open3dengineering/Prusa-i3/Manual/media/assembed_parts/x3.png

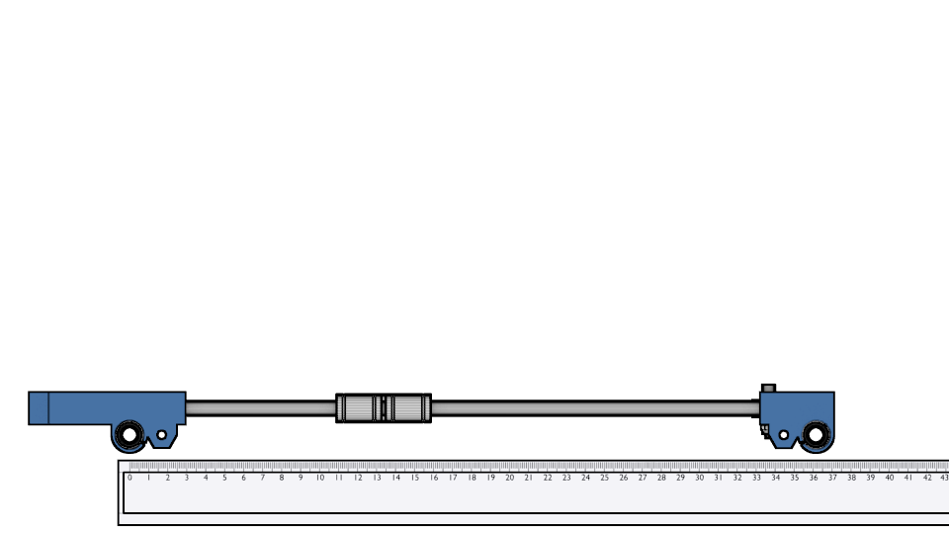
Manual/media/assembed_parts/x3.png
