open3dengineering/Prusa-i3/Manual/media/assembed_parts/x6.png

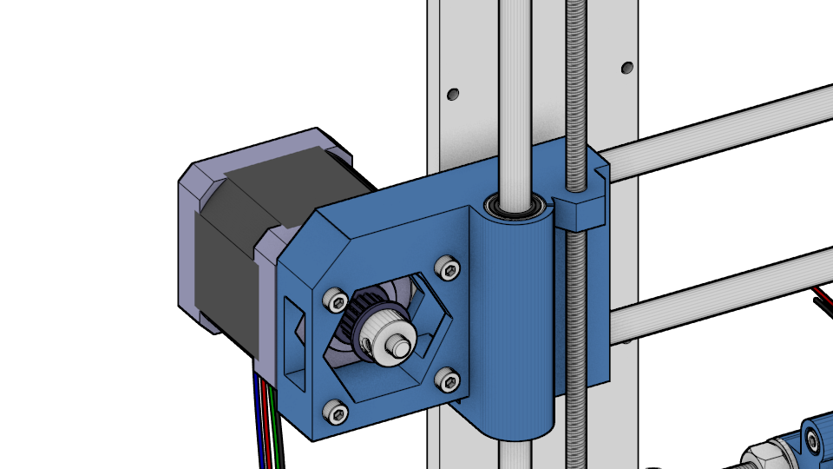
Manual/media/assembed_parts/x6.png
