open3dengineering/Prusa-i3/Manual/media/assembed_parts/x.png

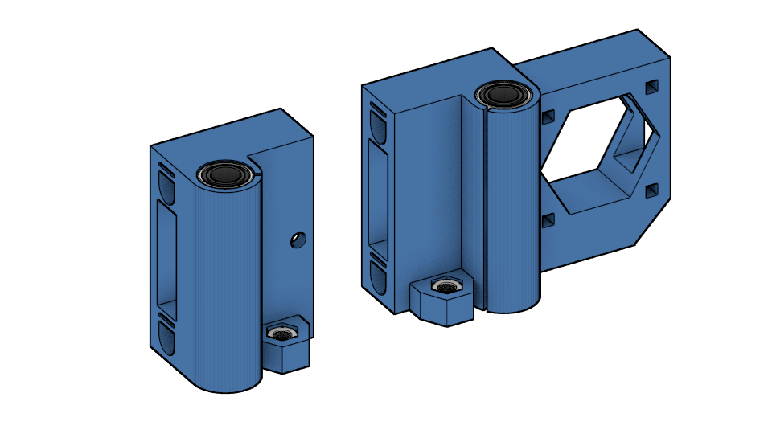
Manual/media/assembed_parts/x.png
