open3dengineering/Prusa-i3/Manual/media/assembed_parts/Y10.png

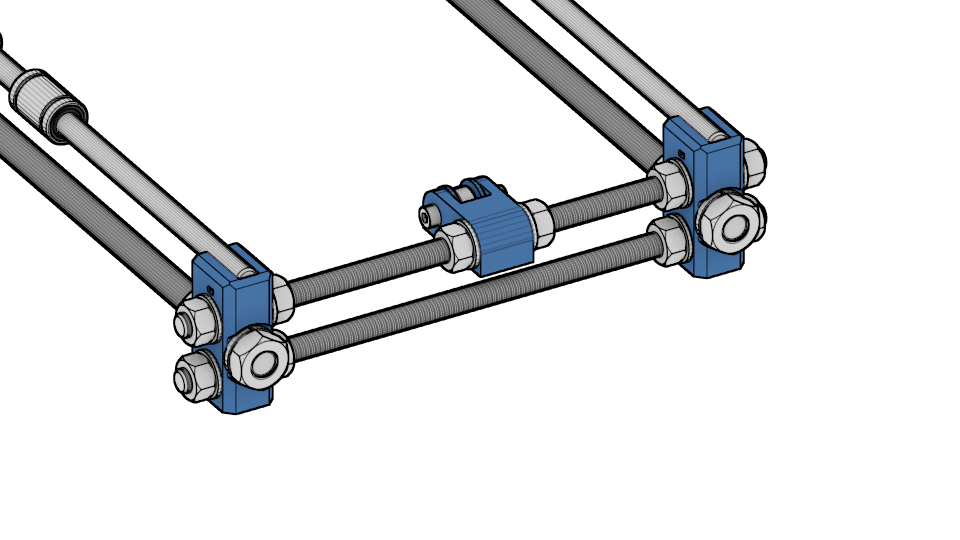
Manual/media/assembed_parts/Y10.png
