open3dengineering/Prusa-i3/Manual/media/assembed_parts/Y13.png

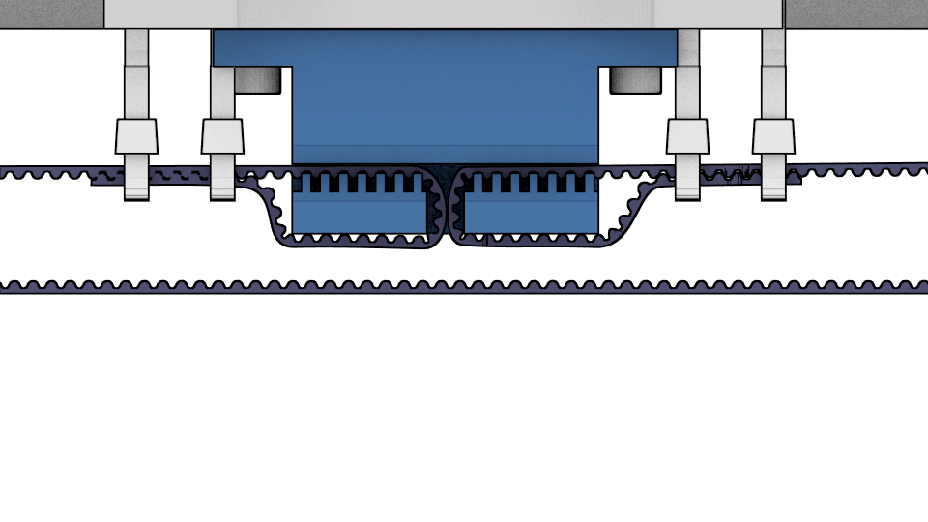
Manual/media/assembed_parts/Y13.png
