open3dengineering/Prusa-i3/Manual/media/assembed_parts/Y14.png

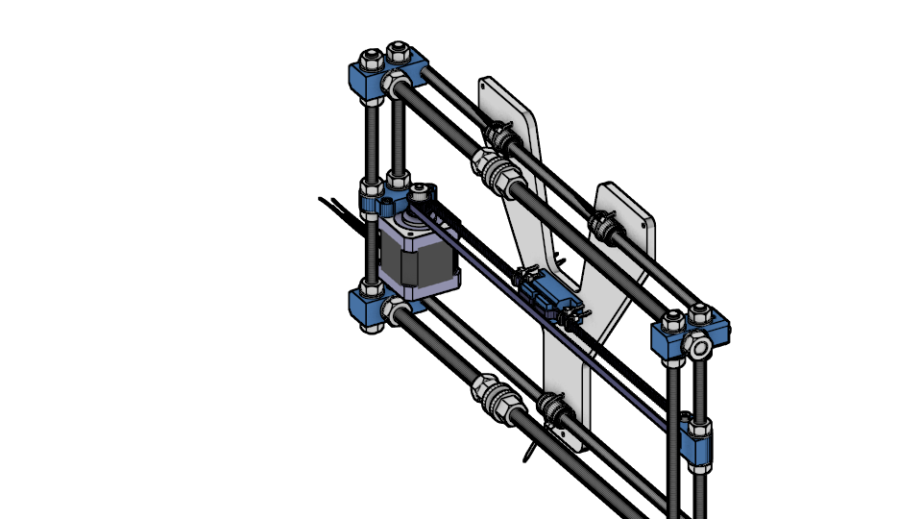
Manual/media/assembed_parts/Y14.png
