open3dengineering/Prusa-i3/Manual/media/assembed_parts/Y15.png

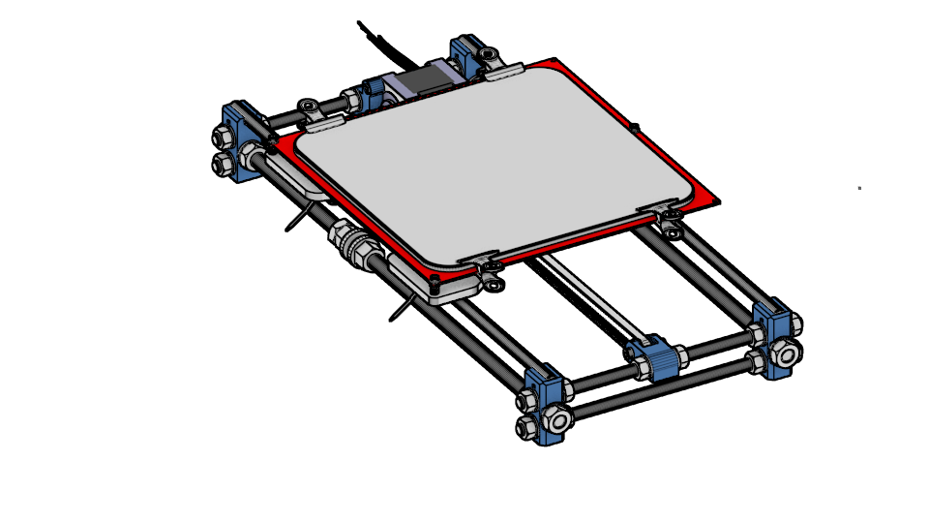
Manual/media/assembed_parts/Y15.png
