open3dengineering/Prusa-i3/Manual/media/assembed_parts/Y16.png

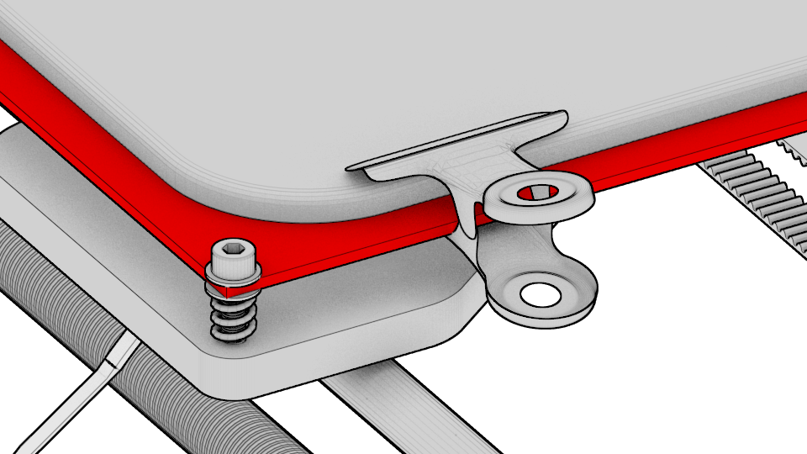
Manual/media/assembed_parts/Y16.png
