open3dengineering/Prusa-i3/Manual/media/assembed_parts/YA1.png

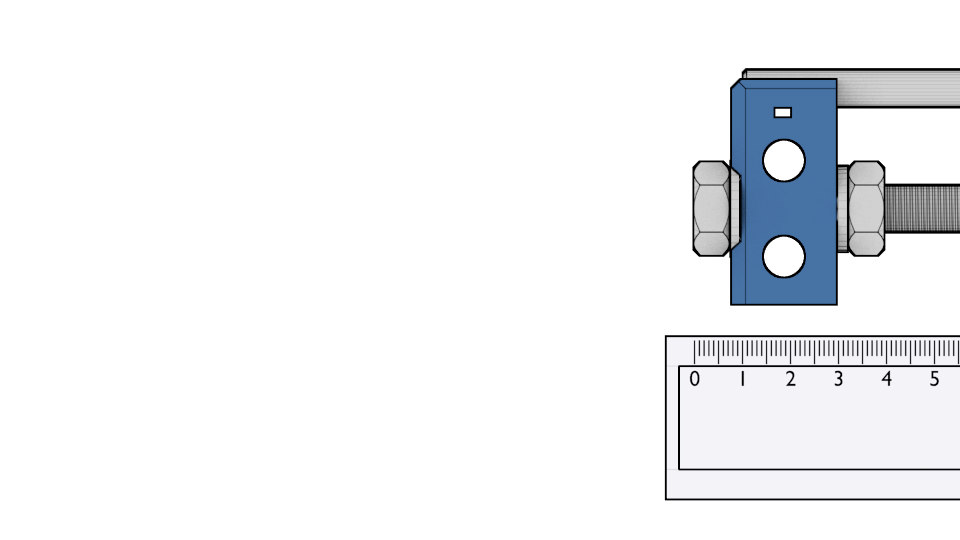
Manual/media/assembed_parts/YA1.png
