open3dengineering/Prusa-i3/Manual/media/assembed_parts/YA4.png

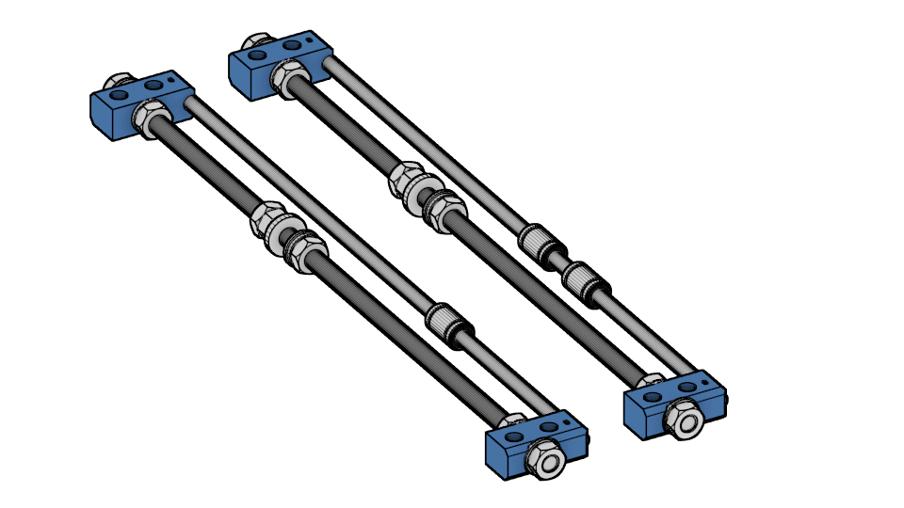
Manual/media/assembed_parts/YA4.png
