open3dengineering/Prusa-i3/Manual/media/assembed_parts/YA.png

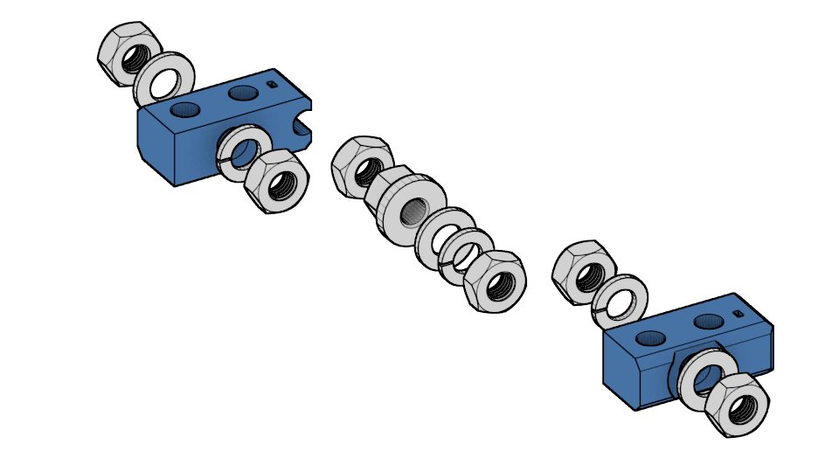
Manual/media/assembed_parts/YA.png
