open3dengineering/Prusa-i3/Manual/media/assembed_parts/z1.png

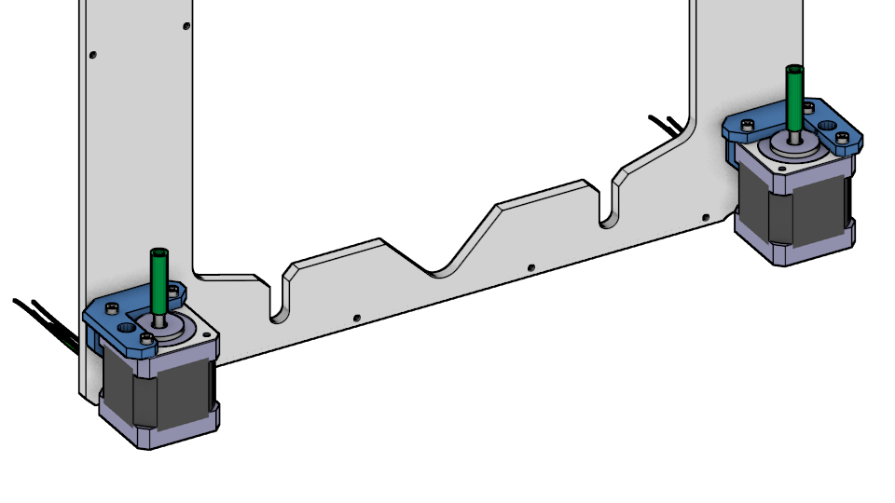
Manual/media/assembed_parts/z1.png
