open3dengineering/Prusa-i3/Manual/media/assembed_parts/z2.png

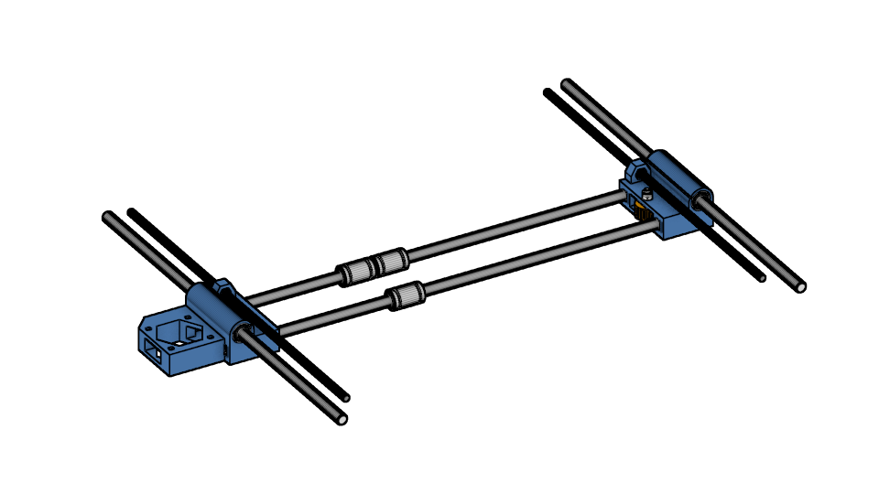
Manual/media/assembed_parts/z2.png
