open3dengineering/Prusa-i3/Manual/media/assembed_parts/z3.png

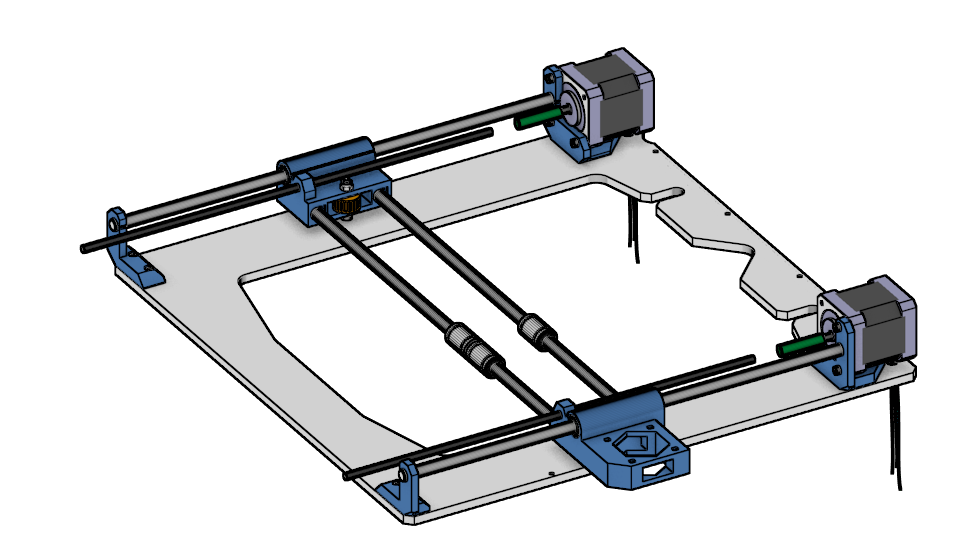
Manual/media/assembed_parts/z3.png
