open3dengineering/Prusa-i3/Manual/media/assembed_parts/z.png

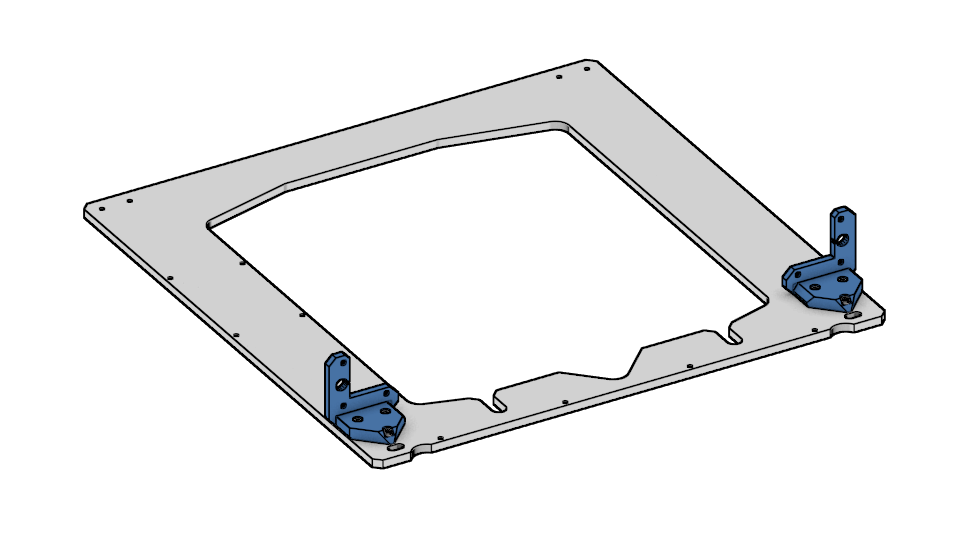
Manual/media/assembed_parts/z.png
