open3dengineering/Prusa-i3/Manual/media/single_parts/608.png

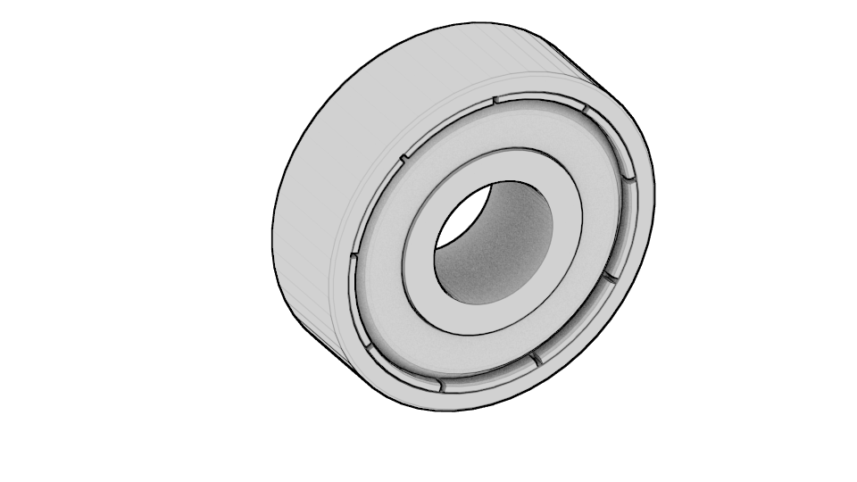
Manual/media/single_parts/608.png
