open3dengineering/Prusa-i3/Manual/media/single_parts/Coupler.png

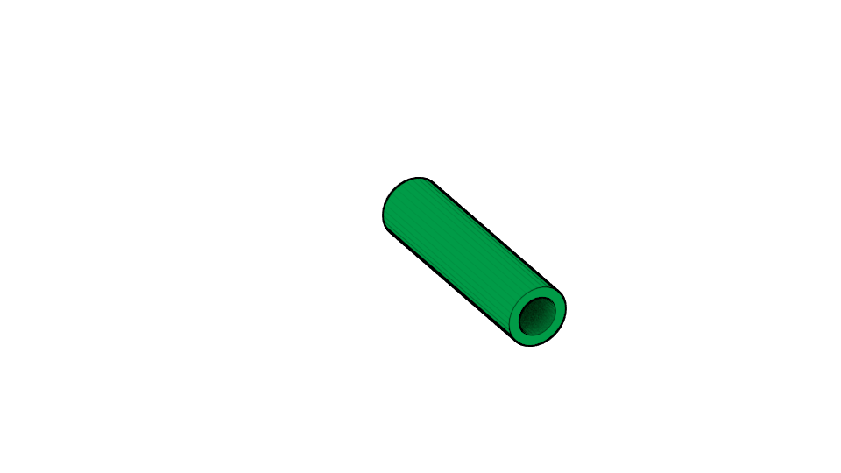
Manual/media/single_parts/Coupler.png
