open3dengineering/Prusa-i3/Manual/media/single_parts/DIN 6331.png

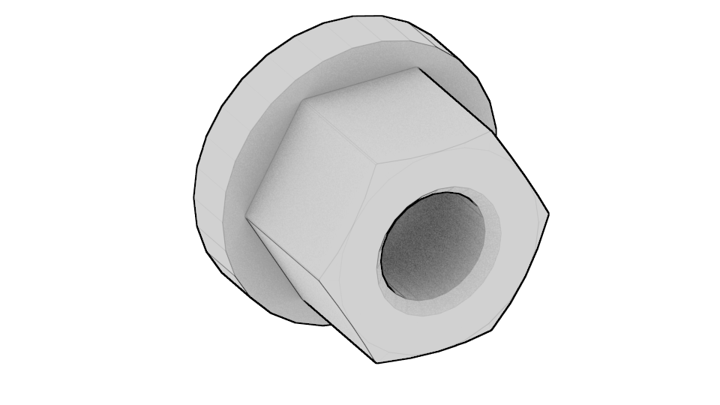
Manual/media/single_parts/DIN 6331.png
