open3dengineering/Prusa-i3/Manual/media/single_parts/GT2 Belt.png

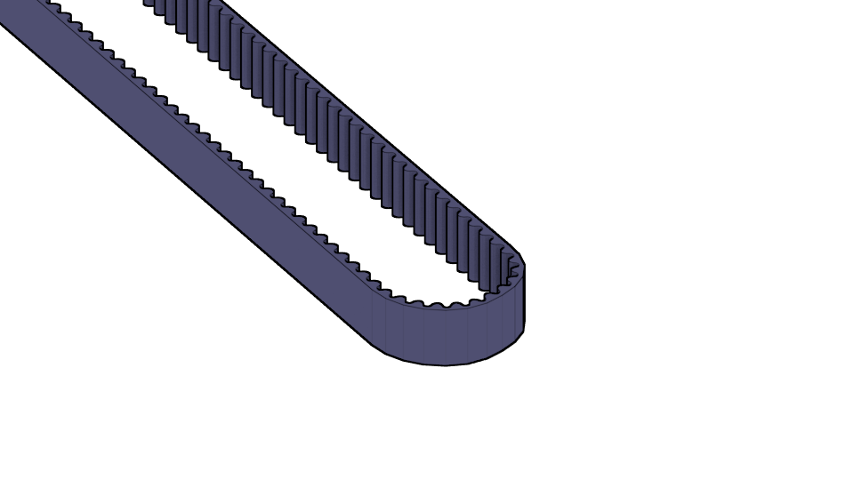
Manual/media/single_parts/GT2 Belt.png
