open3dengineering/Prusa-i3/Manual/media/single_parts/LM8UU.png

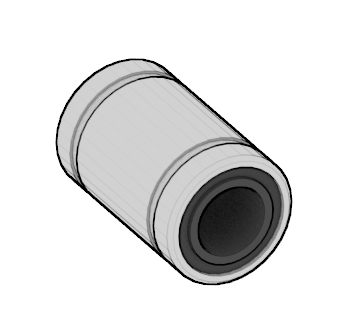
Manual/media/single_parts/LM8UU.png
