open3dengineering/Prusa-i3/Manual/media/single_parts/M3x10.png

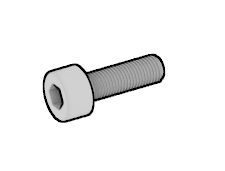
Manual/media/single_parts/M3x10.png
