open3dengineering/Prusa-i3/Manual/media/single_parts/M4 Nyloc.png

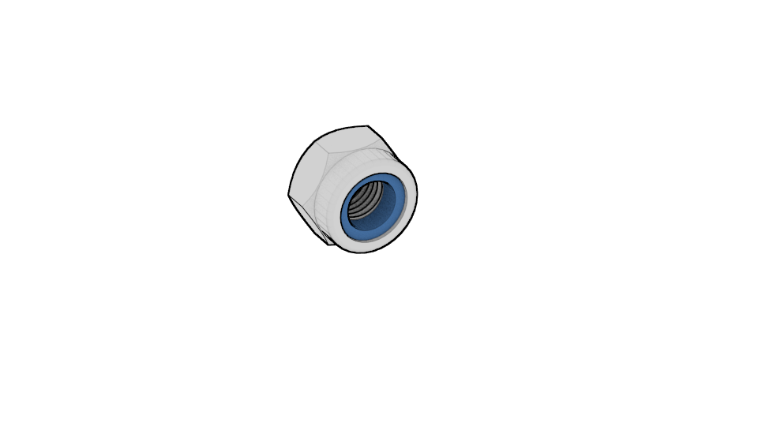
Manual/media/single_parts/M4 Nyloc.png
