open3dengineering/Prusa-i3/Manual/media/single_parts/M4 x 20.png

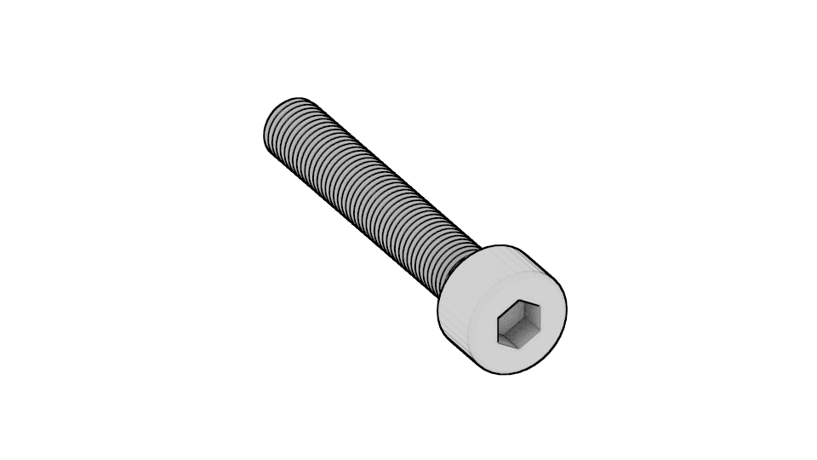
Manual/media/single_parts/M4 x 20.png
