open3dengineering/Prusa-i3/Manual/media/single_parts/M8 washer.png

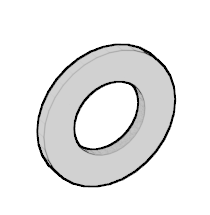
Manual/media/single_parts/M8 washer.png
