open3dengineering/Prusa-i3/Manual/media/single_parts/M8 washerbig.png

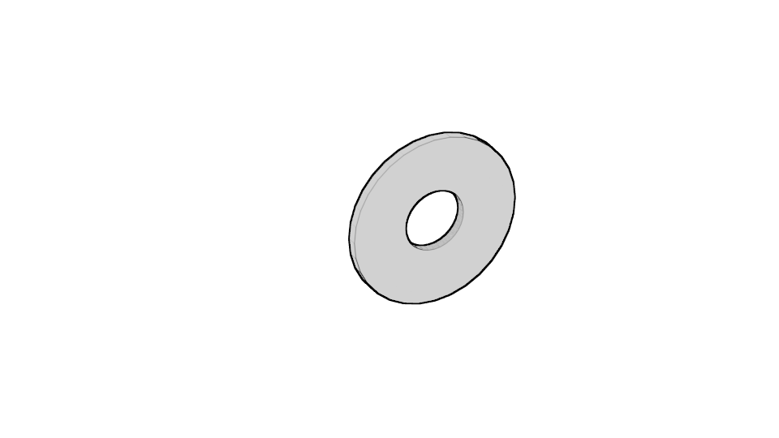
Manual/media/single_parts/M8 washerbig.png
