open3dengineering/Prusa-i3/Manual/media/single_parts/mauly.png

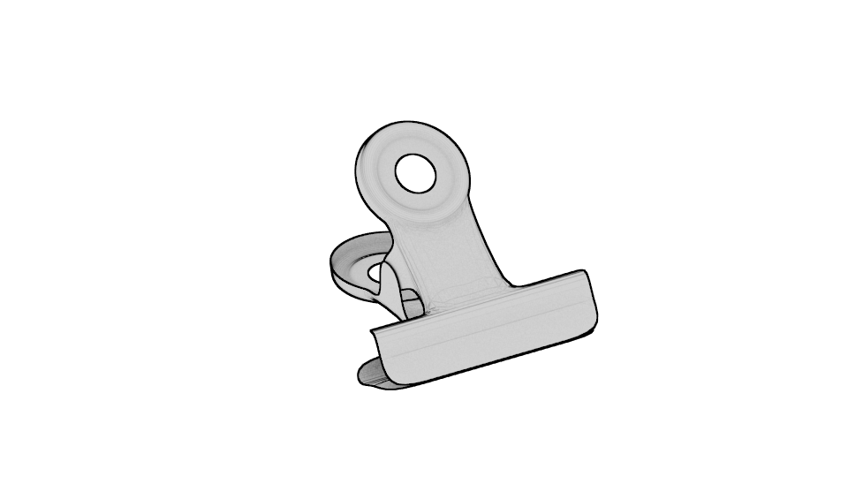
Manual/media/single_parts/mauly.png
