open3dengineering/Prusa-i3/Manual/media/single_parts/motor holder.png

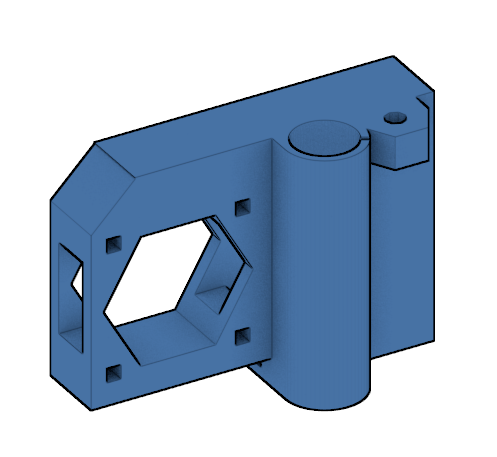
Manual/media/single_parts/motor holder.png
