open3dengineering/Prusa-i3/Manual/media/single_parts/Nema 17 stepper.png

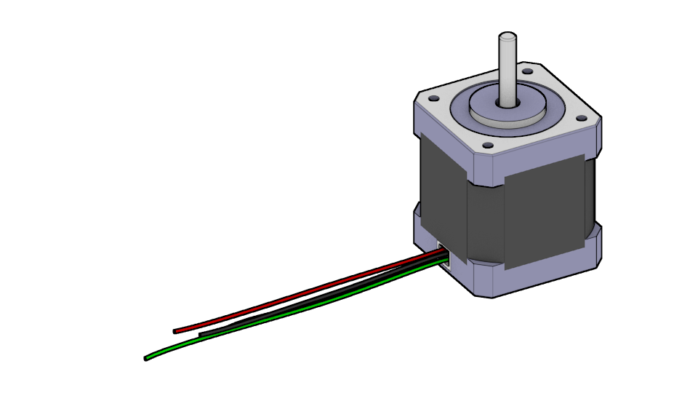
Manual/media/single_parts/Nema 17 stepper.png
