open3dengineering/Prusa-i3/Manual/media/single_parts/pulley.png

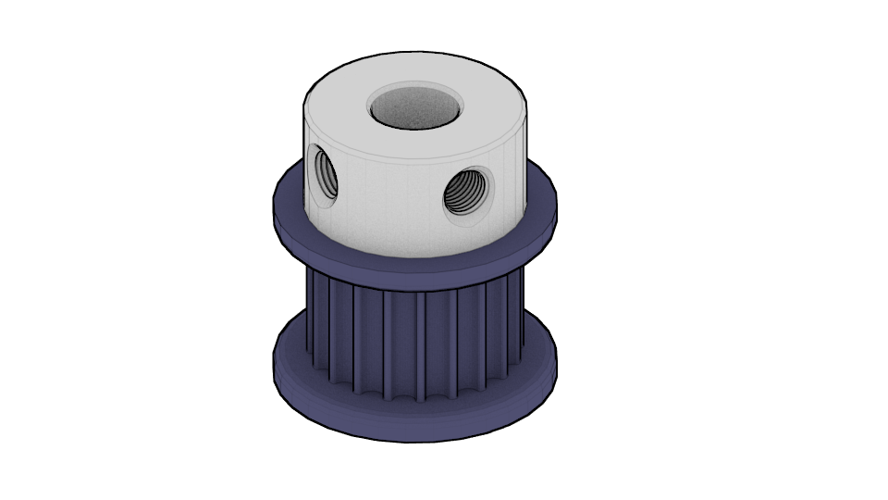
Manual/media/single_parts/pulley.png
