open3dengineering/Prusa-i3/Manual/media/single_parts/Smooth rod y.png

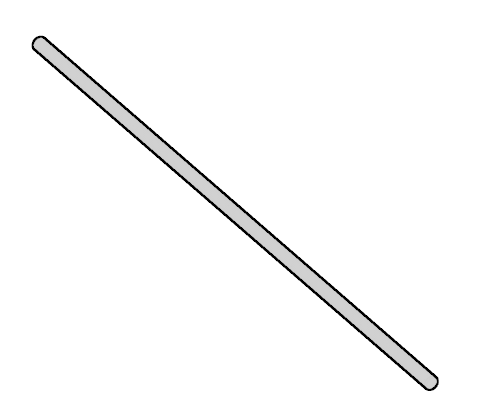
Manual/media/single_parts/Smooth rod y.png
