open3dengineering/Prusa-i3/Manual/media/single_parts/smoothrod.png

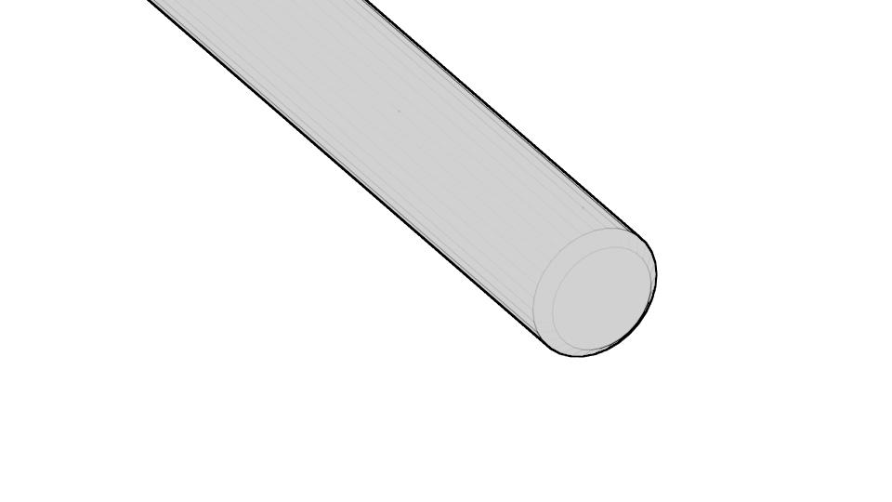
Manual/media/single_parts/smoothrod.png
