open3dengineering/Prusa-i3/Manual/media/single_parts/SpringWasher.png

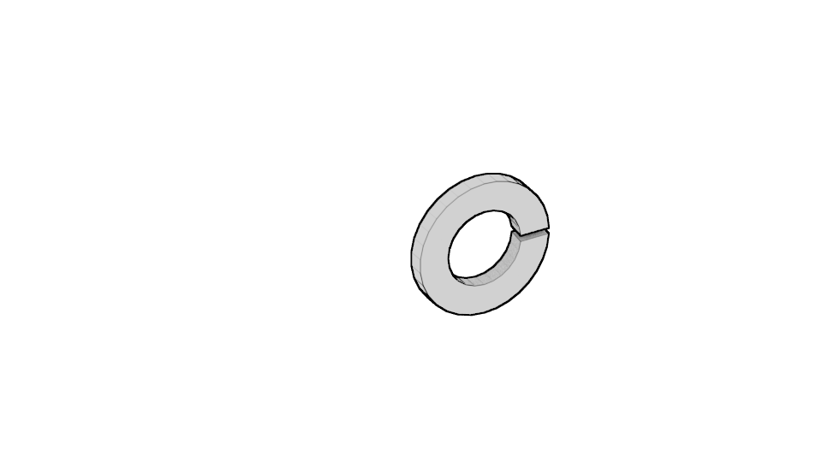
Manual/media/single_parts/SpringWasher.png
