open3dengineering/Prusa-i3/Manual/media/single_parts/Threaded rod x.png

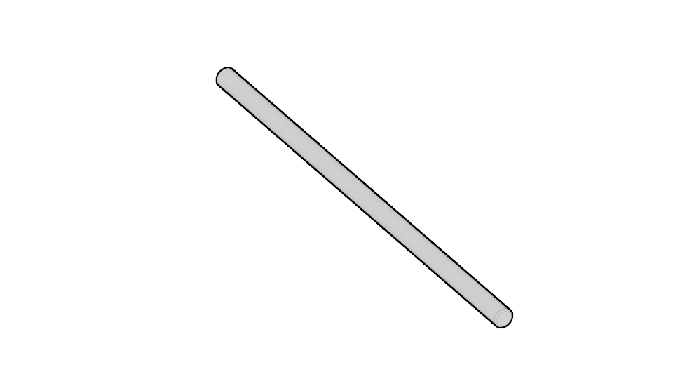
Manual/media/single_parts/Threaded rod x.png
