open3dengineering/Prusa-i3/Manual/media/single_parts/threadedrod M10.png

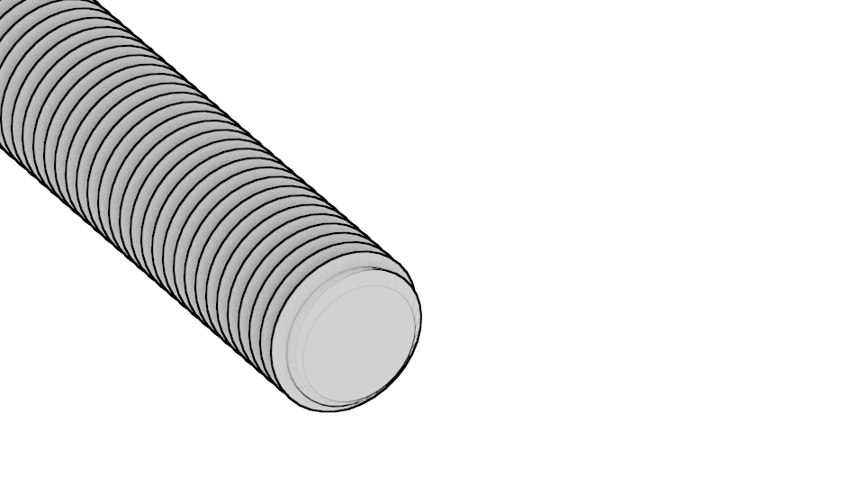
Manual/media/single_parts/threadedrod M10.png
