open3dengineering/Prusa-i3/Manual/media/single_parts/washer M3.png

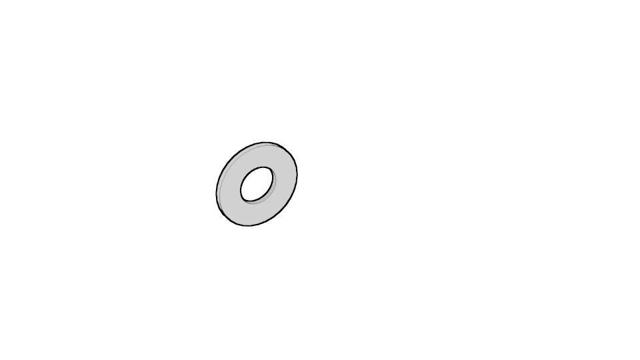
Manual/media/single_parts/washer M3.png
