open3dengineering/Prusa-i3/Manual/media/single_parts/x-motor.png

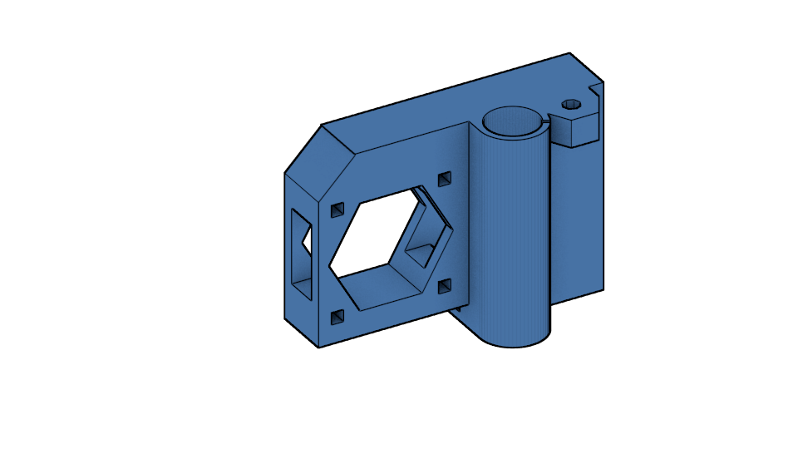
Manual/media/single_parts/x-motor.png
