open3dengineering/Prusa-i3/Manual/media/single_parts/XZ Plat1.png

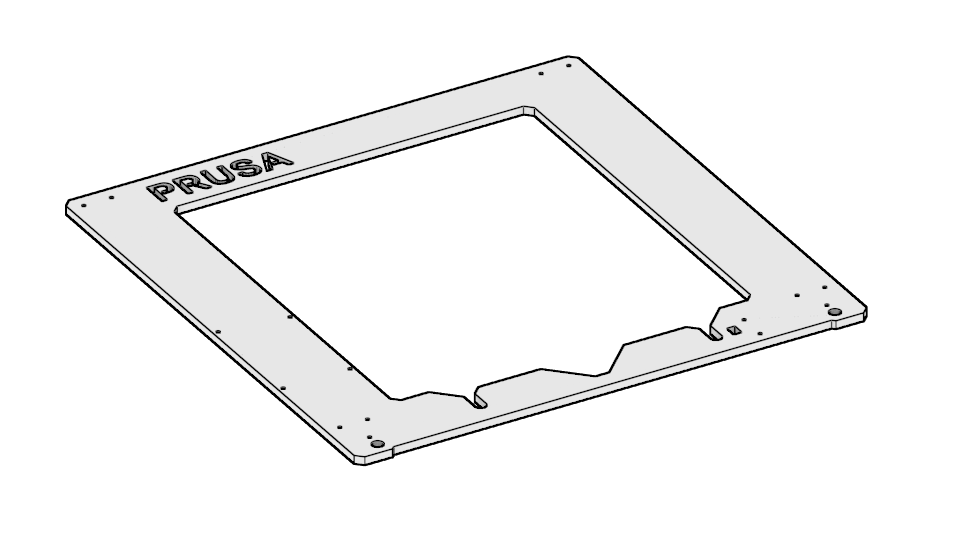
Manual/media/single_parts/XZ Plat1.png
