open3dengineering/Prusa-i3/Manual/media/single_parts/xz plate2.png

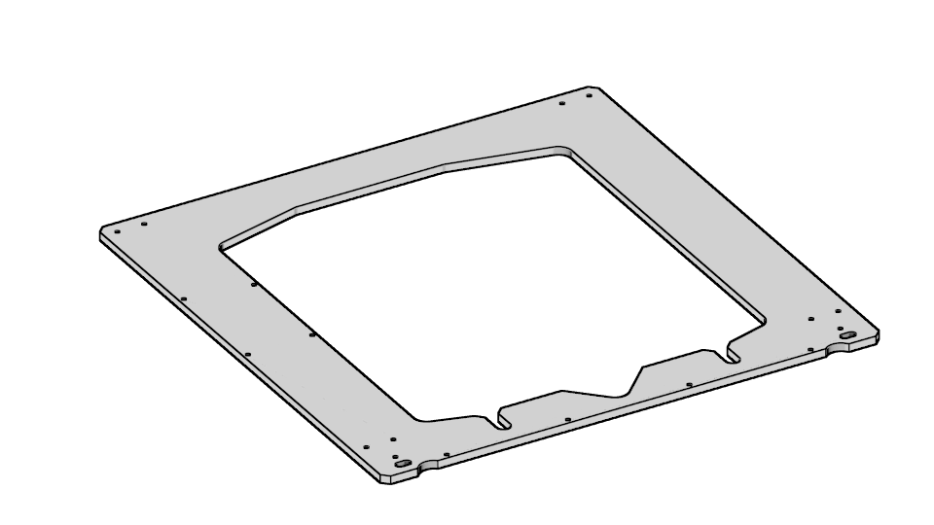
Manual/media/single_parts/xz plate2.png
