open3dengineering/Prusa-i3/Manual/media/single_parts/y belt holder.png

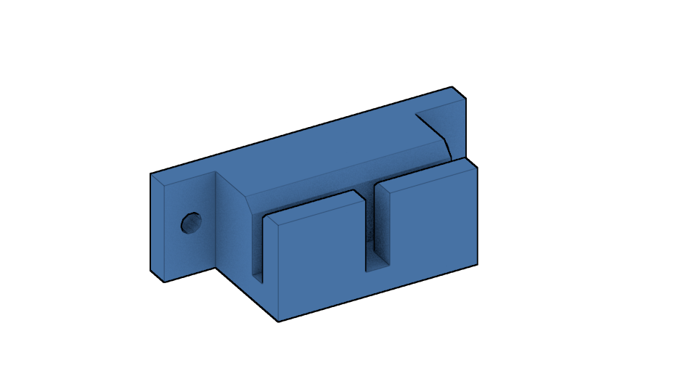
Manual/media/single_parts/y belt holder.png
