open3dengineering/Prusa-i3/Manual/media/single_parts/y plate.png

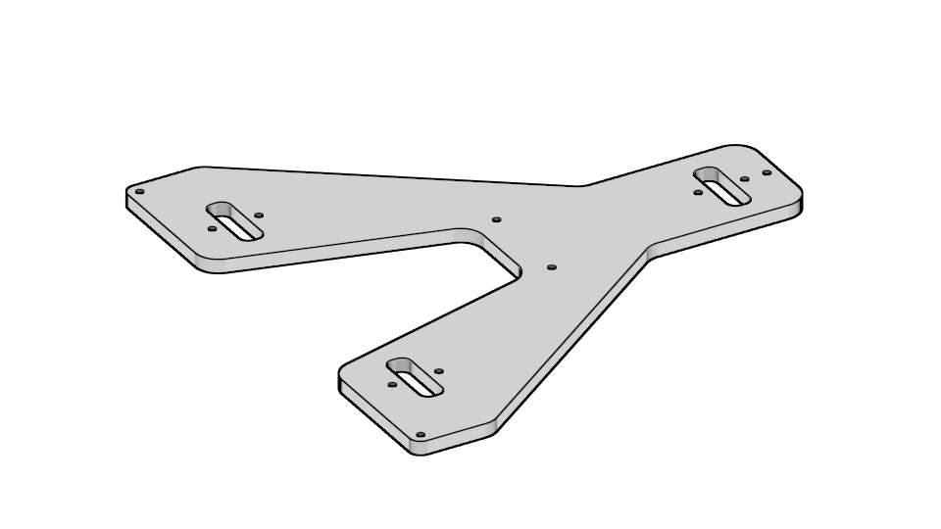
Manual/media/single_parts/y plate.png
