open3dengineering/Prusa-i3/Manual/media/single_parts/y-Corner1.png

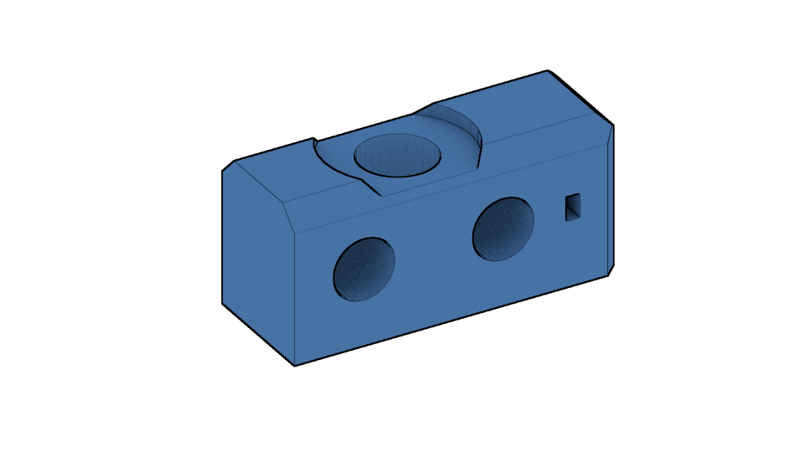
Manual/media/single_parts/y-Corner1.png
