open3dengineering/Prusa-i3/Manual/media/single_parts/Y-Corner.png

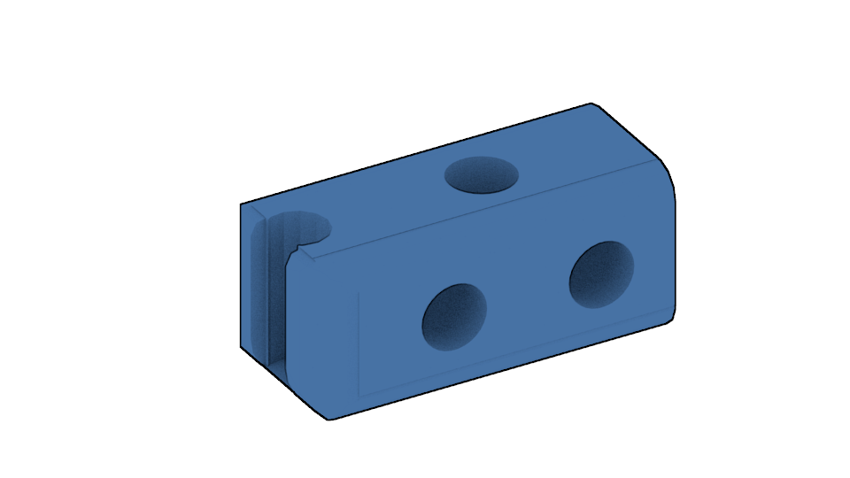
Manual/media/single_parts/Y-Corner.png
