open3dengineering/Prusa-i3/Manual/media/single_parts/y-idler.png

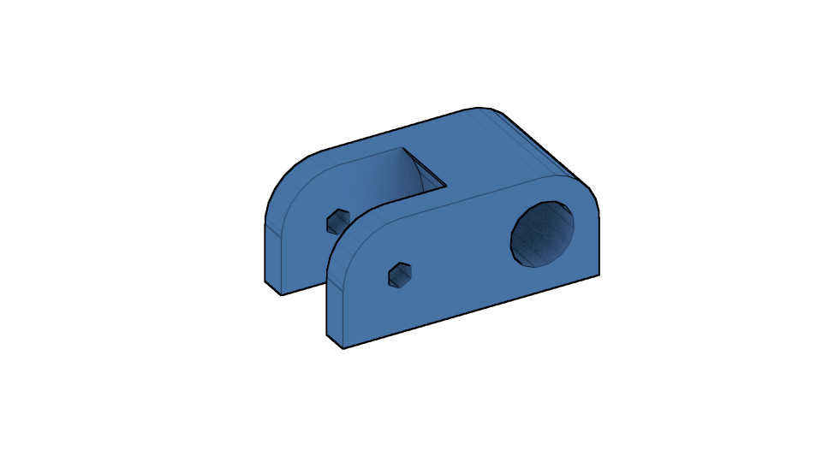
Manual/media/single_parts/y-idler.png
