open3dengineering/Prusa-i3/Manual/media/single_parts/y-motor.png

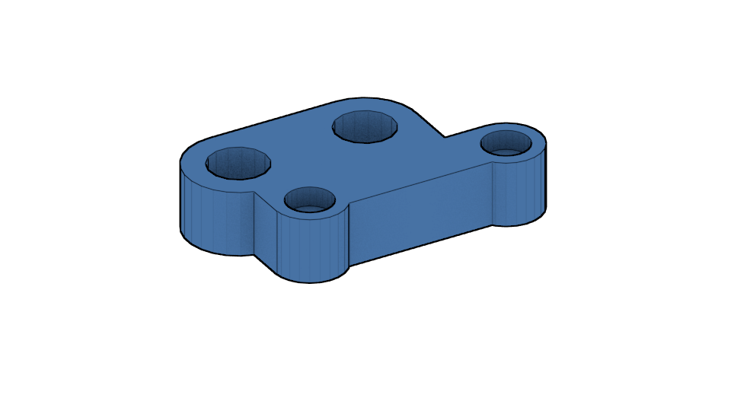
Manual/media/single_parts/y-motor.png
