open3dengineering/Prusa-i3/Manual/media/single_parts/Z-Bottom L.png

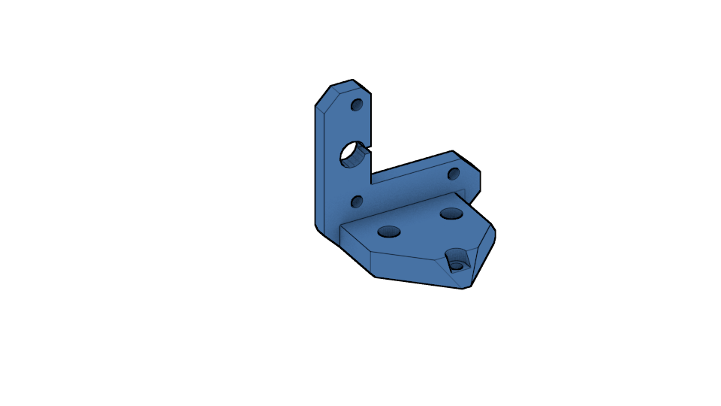
Manual/media/single_parts/Z-Bottom L.png
