open3dengineering/Prusa-i3/Manual/media/single_parts/Z-Top L.png

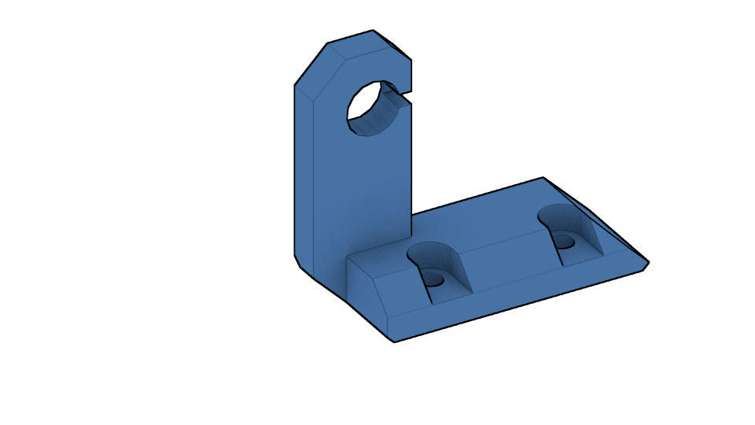
Manual/media/single_parts/Z-Top L.png
