open3dengineering/Prusa-i3/Manual/media/single_parts/ziptie.png

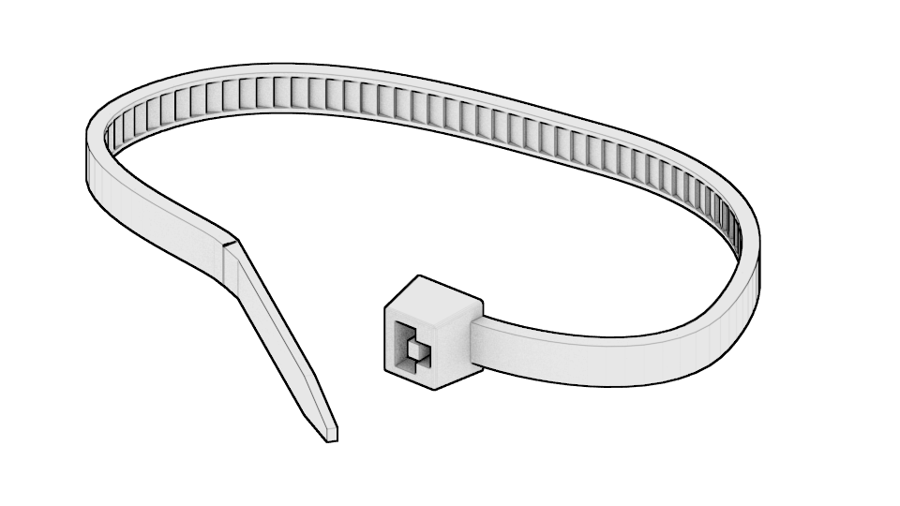
Manual/media/single_parts/ziptie.png
