open3dengineering/Prusa-i3/Stl/endstop-holder-top.stl

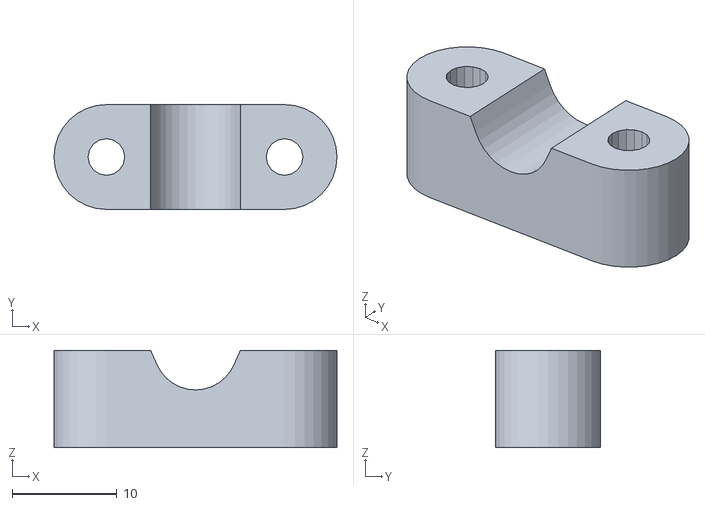
[picture p78: CAD file, 2013-04-30]
Stl/endstop-holder-top.stl
27.0 x 10.0 x 9.27
