open3dengineering/Prusa-i3/Stl/y-idler.stl

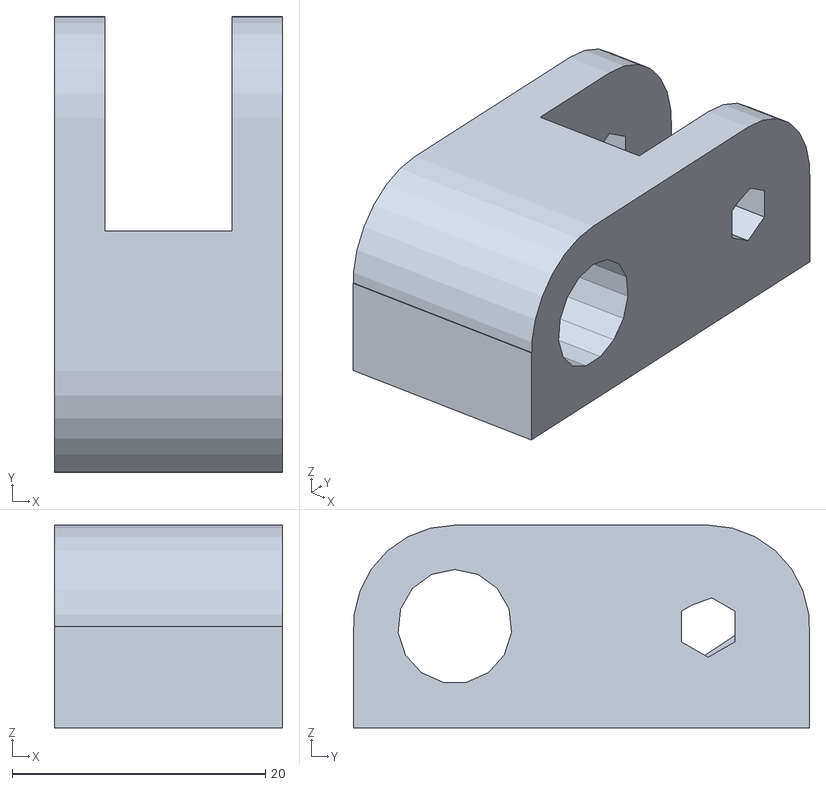
[picture p79: CAD file, 2013-04-30]
Stl/y-idler.stl
18.0 x 36.0 x 16.0
