open3dengineering/Prusa-i3/Stl/belt-guides.stl

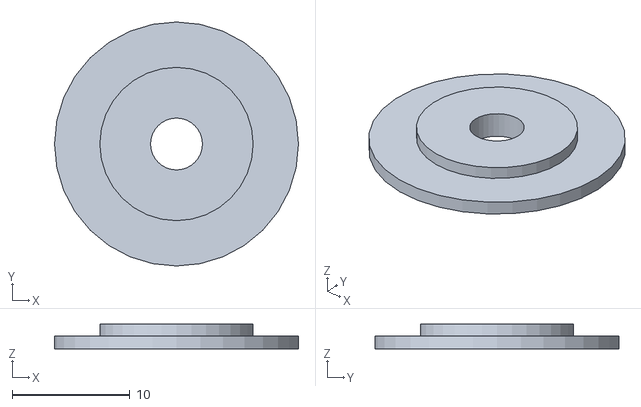
[picture p80: CAD file, 2013-04-30]
Stl/belt-guides.stl
20.7 x 20.7 x 2.10
