open3dengineering/Prusa-i3/Stl/endstop-holder-bottom.stl

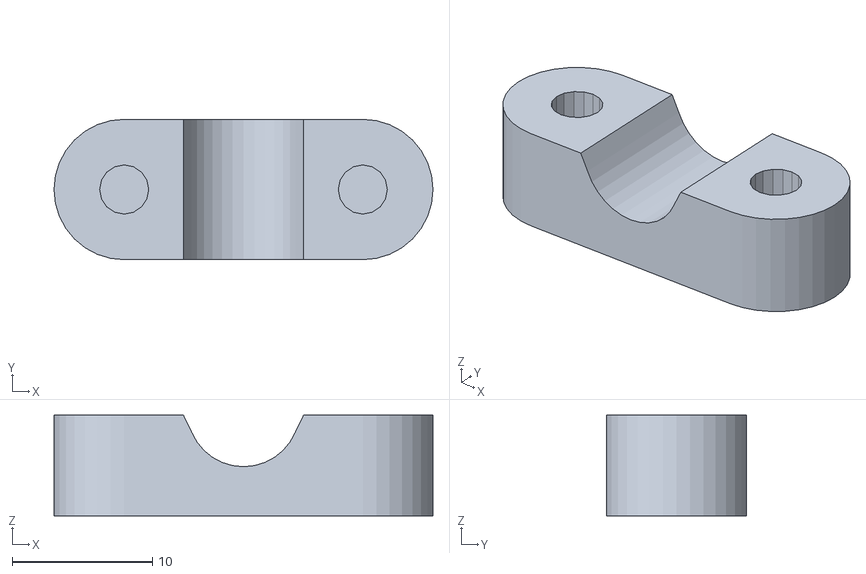
[picture p81: CAD file, 2013-04-30]
Stl/endstop-holder-bottom.stl
27.0 x 10.0 x 7.17
