open3dengineering/Prusa-i3/Stl/y-beltholder-gt2.stl

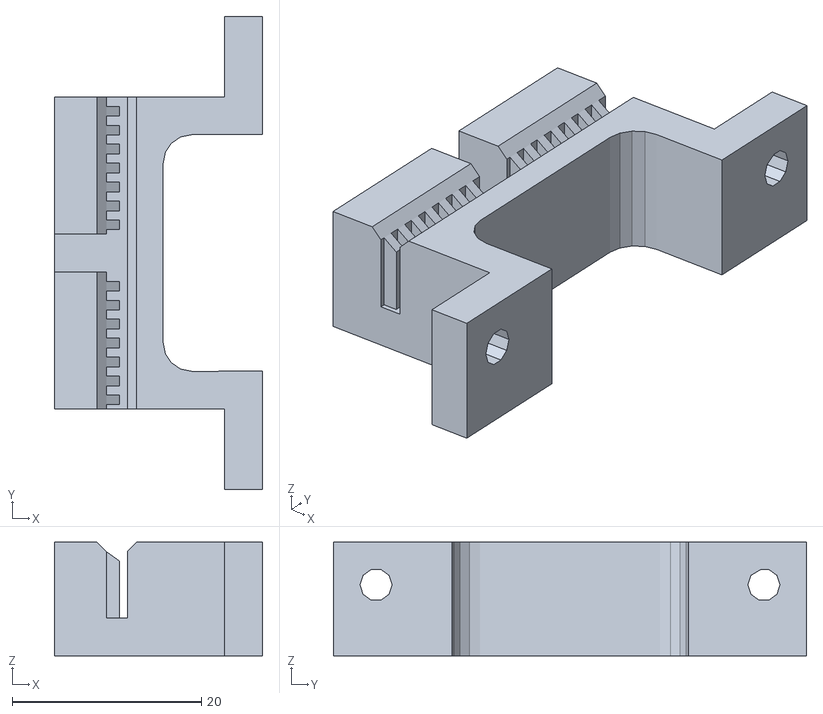
[picture p82: CAD file, 2013-04-30]
Stl/y-beltholder-gt2.stl
22.0 x 50.0 x 12.0
